curiouselectric/SensorInterfaceBoard/Sensor Interface Board Firmware/ATMega328_Sensor_Interface_Firmware_v4/average_data.h

#pragma once

#include <stdio.h>
#include <Arduino.h>
#include "config.h"

class data_channel {
public:
  char id;  // This is used to identify what the type of data is in this channel: eg T for temp, H for humidity, etc. // NOT YET IMPLEMENTED

  int data_send_time;  // This holds a value of when to check the sensor and update the data values (0 = 0.1S,  1 = 1S, 2 = 10S, 3 = 60S, 4 = 600S, 5 = 3600S)

  float data_1s;
  float data_10s;
  float data_60s;
  float data_600s;
  float data_3600s;
  float data_min;  // Holds the minimum value ever recorded until reset
                   // Once read and recorded then this value is reset
  float data_max;  // Holds the maximum value ever recorded until reset
                   // Once read and recorded then this value is reset

  float data_1s_holder;
  float data_10s_holder;
  float data_60s_holder;
  float data_600s_holder;
  float data_3600s_holder;

#ifdef WIND_SENSOR
  float wind_speed_conv_m;  // The conversion is y=mx+c, with the m and c here.
  float wind_speed_conv_c;
#endif
  
  // This is the constructor
  data_channel() {
    data_send_time = 0;
    data_1s = 0;
    data_10s = 0;
    data_60s = 0;
    data_600s = 0;
    data_3600s = 0;
    data_min = 99999;
    data_max = -99999;
  }
};
