curiouselectric/SensorInterfaceBoard/Sensor Interface Board Firmware/ATMega328_Sensor_Interface_Firmware_v4/pulse_counter.h

#pragma once

#include <stdio.h>
#include <Arduino.h>
#include "config.h"

#ifdef WIND_SENSOR

class pulse_counter_ {
  public:
    volatile uint32_t pulse_counter_1 = 0;
    uint32_t prev_pulse_counter_1 = 0; 
};

#endif
